akuehlewind/ESPHome-Fingerprint-Display-VideoDoorbell/esphome/images/doorbell-background-plain.jpg

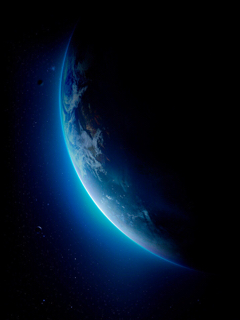
esphome/images/doorbell-background-plain.jpg
