akuehlewind/ESPHome-Fingerprint-Display-VideoDoorbell/images/back.jpeg

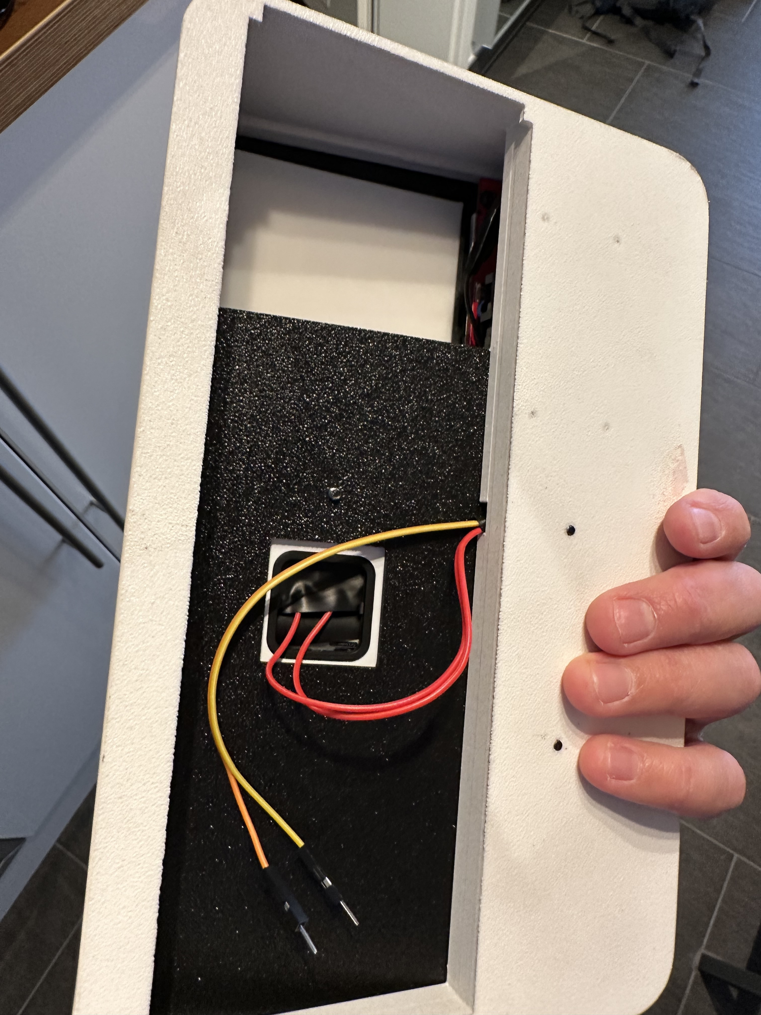
images/back.jpeg
