akuehlewind/ESPHome-Fingerprint-Display-VideoDoorbell/images/doorbell1.jpeg

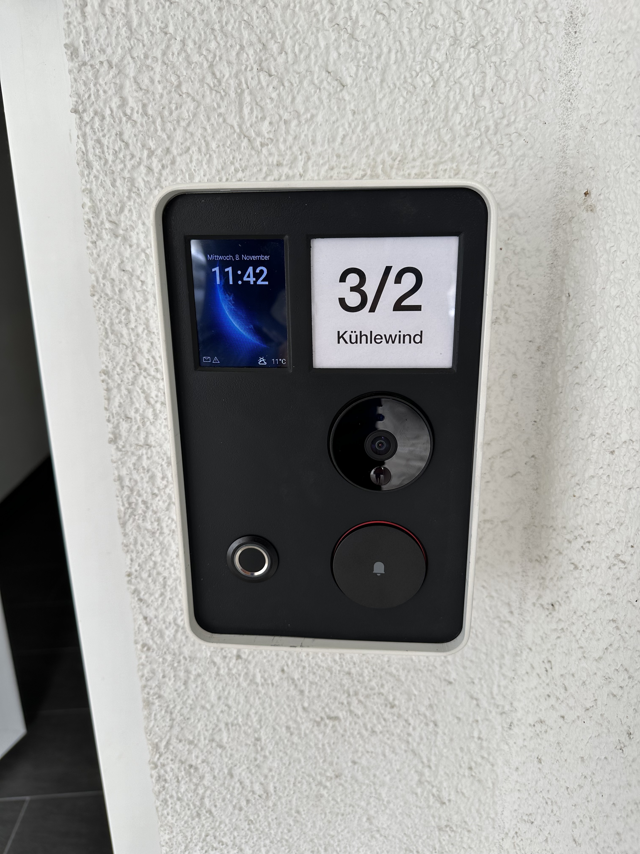
images/doorbell1.jpeg
