akuehlewind/ESPHome-Fingerprint-Display-VideoDoorbell/images/inside1.jpeg

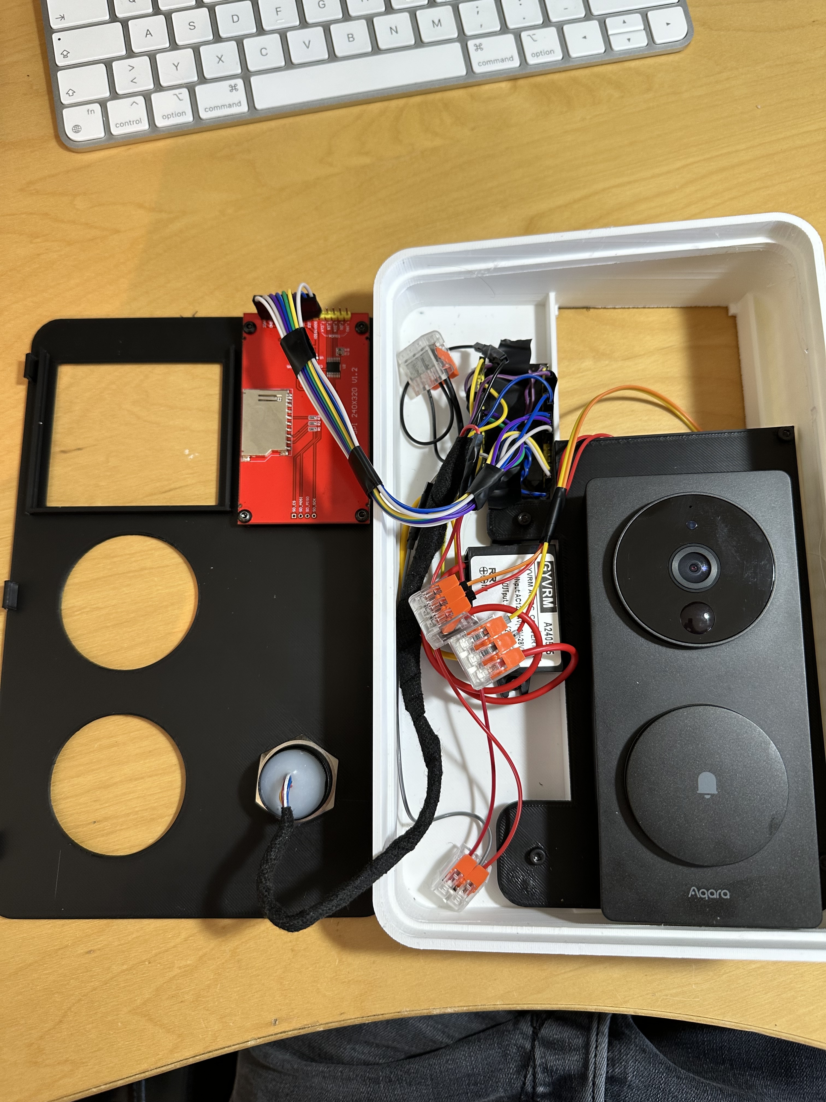
images/inside1.jpeg
