akuehlewind/ESPHome-Fingerprint-Display-VideoDoorbell/images/notification1.jpeg

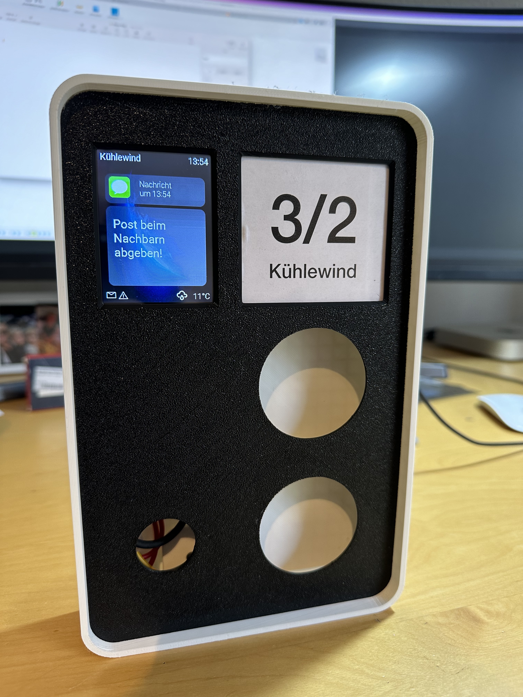
images/notification1.jpeg
