akuehlewind/ESPHome-Fingerprint-Display-VideoDoorbell/images/wiring2.jpeg

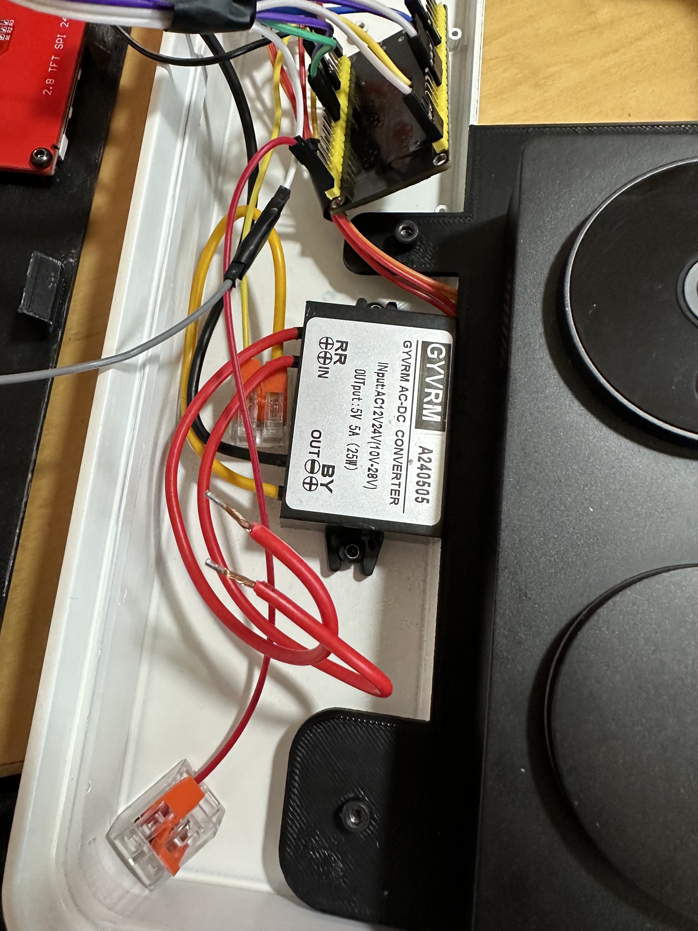
images/wiring2.jpeg
