akuehlewind/ESPHome-Fingerprint-Display-VideoDoorbell/images/wiring.jpeg

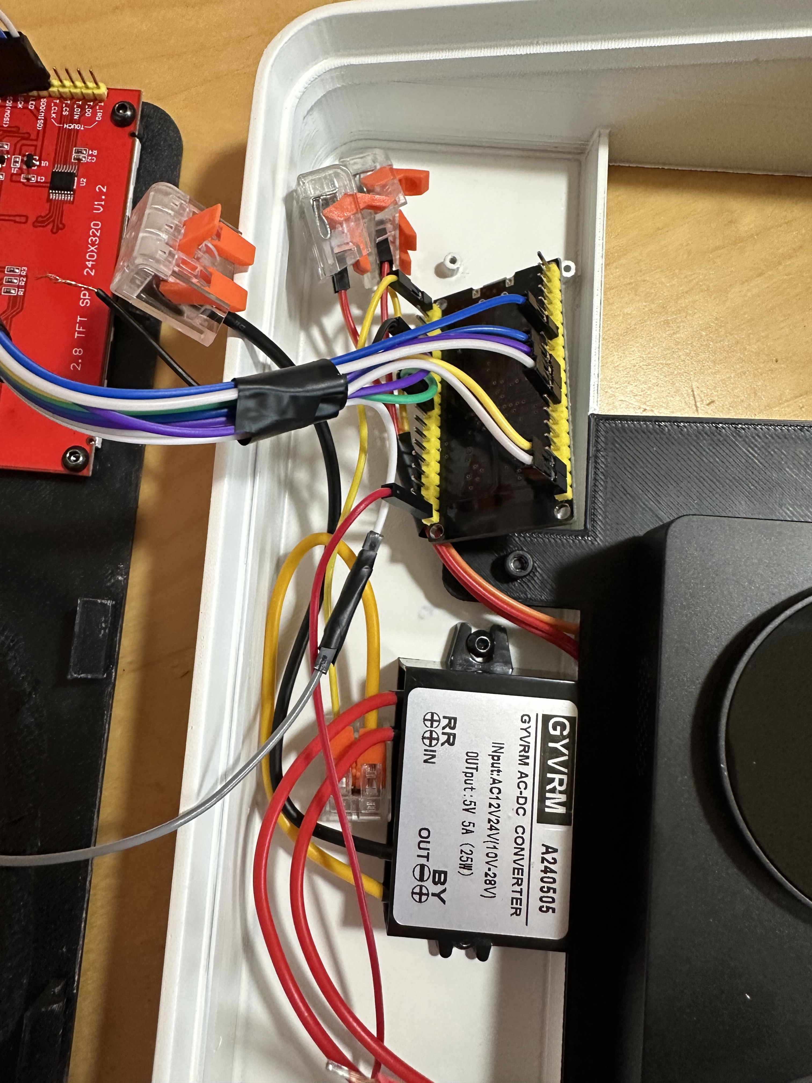
images/wiring.jpeg
